fm4dd/gm-study-e1/examples/buzzer/src/hexdigit.v

module hexdigit(
  input wire [4:0] in,
  input wire dp,
  output reg [7:0] out
  );

// ---------- 7-seg assignment ----------
//                            a
//       d╶┐┌╴c              ────
//      e╶┐││┌╴b          f │    │
//     f╶┐││││┌╴a           │  g │ b
//    g╶┐││││││┌╴dp   ❯❯     ────
//   8'b00000000          e │    │
//                          │    │ c
//                           ────
//                             d   o dp
always @* begin
  out = 8'b11111111;
	 
  case(in)
    4'h0: begin // hex '0' SSD display pattern
      out[7] = 1'b1;
      out[6] = 1'b0;
      out[5] = 1'b0;
      out[4] = 1'b0;
      out[3] = 1'b0;
      out[2] = 1'b0;
      out[1] = 1'b0;
      out[0] = ~dp;
    end
	 
    4'h1: begin // hex '1' SSD display pattern
      out[7] = 1'b1;
      out[6] = 1'b1;
      out[5] = 1'b1;
      out[4] = 1'b1;
      out[3] = 1'b0;
      out[2] = 1'b0;
      out[1] = 1'b1;
      out[0] = ~dp;
    end

    4'h2: begin // hex '2' SSD display pattern
      out[7] = 1'b0;
      out[6] = 1'b1;
      out[5] = 1'b0;
      out[4] = 1'b0;
      out[3] = 1'b1;
      out[2] = 1'b0;
      out[1] = 1'b0;
      out[0] = ~dp;
    end
	 
    4'h3: begin // hex '3' SSD display pattern
      out[7] = 1'b0;
      out[6] = 1'b1;
      out[5] = 1'b1;
      out[4] = 1'b0;
      out[3] = 1'b0;
      out[2] = 1'b0;
      out[1] = 1'b0;
      out[0] = ~dp;
    end
 
     4'h4: begin // hex '4' SSD display pattern
      out[7] = 1'b0;
      out[6] = 1'b0;
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
      out[0] =  ~dp;
    end
    5'b10000: out = 8'b00000000; // 16 = all led on
    5'b10001: out = 8'b01111111; // 17 = - (minus sign)
    5'b10010: out = 8'b11101111; // 18 = _ (underscore)
    5'b10011: out = 8'b10100101; // 19 = S
    default: out = 8'b11111111;
  endcase
end
endmodule
